mincrmatt12/MSign/esp/main/main.cpp

#include "serial.h"
#include "config.h"
#include "webui.h"
#include "wifitime.h"
#include "upd.h"
#include "sd.h"
#include "config.h"
#include "grabber/grab.h"
#include "webui.cfg.h"

#include <esp_log.h>
#include <esp_system.h>
#include <FreeRTOS.h>
#include <task.h>

#ifndef SIM
#include <esp_wifi.h>
#endif

const static char * const TAG = "app_main";

#ifdef SIM
#define STACK_MULT 8
#else
#define STACK_MULT 1
#endif

int msign_putchar_preservicer(int c) {
	sd::log_putc(c);
#ifdef SIM
	return fputc(c, stderr);
#else
	return putchar(c);
#endif
}

int msign_putchar(int c) {
	sd::log_putc(c);
	if (serial::interface.is_sleeping()) return c;
#ifdef SIM
	return fputc(c, stderr);
#else
	return putchar(c);
#endif
}

extern "C" void app_main() {
	ESP_LOGI(TAG, "Starting MSign...");

	// Try and start the SD layer
	switch (sd::init()) {
		case sd::InitStatus::NoCard:
			ESP_LOGE(TAG, "=============================");
			ESP_LOGE(TAG, "No card is inserted! Halting!");
			ESP_LOGE(TAG, "=============================");
			return;
		case sd::InitStatus::UnusableCard:
		case sd::InitStatus::UnkErr:
			ESP_LOGE(TAG, "Unusable/unknown error while initializing the card.");
			return;
		case sd::InitStatus::FormatError:
			ESP_LOGE(TAG, "No filesystem on card");
			// TODO: maybe indicate these failures to the STM somehow?
			return;
		default:
			break;
	}

	// check for updates
	switch (upd::needed()) {
		case upd::FULL_SYSTEM:
			upd::update_system();
			ESP_LOGW(TAG, "somehow returned from update_system? restarting anyways.");
			esp_restart();
			break;
		case upd::CERTIFICATE_FILE:
			upd::update_cacerts();
			esp_restart();
			break;
		default:
			break;
	}

	// Install logger
	sd::init_logger();
	esp_log_set_putchar(msign_putchar_preservicer);

	bool had_crash = serial::process_stored_crashlogs();
	serial::interface.init();

	esp_log_set_putchar(msign_putchar);

	// Create event handle early
	wifi::events = xEventGroupCreate();
	xEventGroupSetBits(wifi::events, wifi::GrabTaskDead);

	// Start up the servicer
	if (xTaskCreate([](void *ptr){
		serial::interface.run((bool)ptr);
	}, "srv", 2048 * STACK_MULT, (void*)had_crash, 9, NULL) != pdPASS) {
		ESP_LOGE(TAG, "Failed to create srv");
		return;
	}


	// Load the config from the SD card
	if (!config::parse_config_from_sd()) {
		return;
	}

	if (!wifi::init()) {
		ESP_LOGE(TAG, "Not starting data services due to no WIFI.");
		// TODO: make this setup softap mode for netcfg
	}

	// Wait till WIFI is ready to start grab tasks (all for memory optimization crapola in wpa2)
	xEventGroupWaitBits(wifi::events, wifi::WifiConnected, false, true, portMAX_DELAY);

	if (webui::mode != webui::WebuiMode::DISABLED) {
		if (xTaskCreate(webui::run, "webUI", 3072 * STACK_MULT, nullptr,  6, NULL) != pdPASS) {
			ESP_LOGE(TAG, "Failed to create webui; running without it");
		}
	}
	else ESP_LOGW(TAG, "webui is disabled");

	grabber::start();

	ESP_LOGI(TAG, "Created tasks (1)");
	ESP_LOGI(TAG, "Free heap available is %d", (int)heap_caps_get_free_size(pvMALLOC_DRAM));
}
