mincrmatt12/MSign/esp/main/dwhttp.cpp

#include "dwhttp.h"
#include "esp_log.h"
#include <cctype>
#include <cstdio>
#include <esp_system.h>
#include <cstdlib>
#include <memory>
#include <string.h>
#include <bearssl.h>

#include <lwip/sockets.h>
#include <lwip/sys.h>
#include <lwip/netdb.h>

extern "C" {
#include <http_client.h>
#include <http_chunked_recv.h>
};

#include <wpabr_bufman.h>

#include <ff.h>

#undef connect
#undef read
#undef write
#undef socket
#undef send
#undef recv
#undef close
#undef bind

#include "common/ver.h"

// shitty HTTP client....
const char *const msign_ua = "MSign/" MSIGN_MAJOR_VERSION_STRING " (ESP8266, entirely unlike Mozilla) screwanalytics/1.0";

namespace dwhttp {
	namespace detail {
		const static char * const TAG = "d_impl";

		namespace adapter {
			const static char * const TAG = "d_adapter";
			struct HttpAdapter {
				bool connect(const char *host, const char* port="80") {
					if (is_connected()) {
						ESP_LOGW(TAG, "httpadapter still connecting, closing");
						close();
					}

					addrinfo hints{};
					addrinfo *result{}, *rp{};
					hints.ai_family = AF_INET;
					hints.ai_socktype = SOCK_STREAM;

					int stat;
					if ((stat = lwip_getaddrinfo(host, port, &hints, &result))) {
						ESP_LOGE(TAG, "gai fail: %s/%d", lwip_strerr(stat), stat);
						return false;
					}

					for (rp = result; rp != nullptr; rp = rp->ai_next) {
						sockno = lwip_socket(rp->ai_family, rp->ai_socktype,
								rp->ai_protocol);
						if (sockno == -1)
							continue;

						if (lwip_connect(sockno, rp->ai_addr, rp->ai_addrlen) != -1)
							break;                  /* Success */

						lwip_close(sockno);
						sockno = -1;
					}

					lwip_freeaddrinfo(result);

					if (rp == nullptr) {
						ESP_LOGE(TAG, "failed to lookup %s", host);
						return false;
					}

					// Set a 5 second rcvtimeo 
					const struct timeval timeout = { 5, 0 };
					lwip_setsockopt(sockno, SOL_SOCKET, SO_RCVTIMEO, &timeout, sizeof(timeout));

					// We are now connected.
					return true;
				}

				ssize_t read(uint8_t *buf, size_t max) {
					size_t amount = 0;
					while (amount < max) {
						auto amt = read_some(buf, max - amount);
						if (amt == -1) return -1;
						amount += amt;
						buf += amount;
					}
					return amount;
				}

				ssize_t read_some(uint8_t *buf, size_t max) {
					int code = lwip_recv(sockno, buf, max, 0);
					if (code >= 0) return code;
					else {
						switch (errno) {
							default:
								lwip_close(sockno);
								[[fallthrough]];
							case EBADF:
								sockno = -1;
								return -1;
						}
					}
				}

				bool write(const uint8_t *buf, size_t length) {
					size_t pos = 0;
					while (pos < length) {
						int code = lwip_send(sockno, buf + pos, length - pos, 0);
						if (code >= 0) {
							pos += code;
						}
						else {
							switch (errno) {
								default:
									lwip_close(sockno);
									[[fallthrough]];
								case EBADF:
									sockno = -1;
									return false;
							}
						}
					}
					return true;
				}

				bool write(const char *buf) {
					return write((const uint8_t *)buf, strlen(buf));
				}

				void close() {
					if (sockno != -1) lwip_close(sockno);
					sockno = -1;
				}

				void flush() {}

				bool is_connected() {
					return sockno != -1;
				}
			protected:
				int sockno = -1;
			};

			struct HeldTA {
				HeldTA(const char *filename) {
					std::unique_ptr<br_x509_decoder_context> ctx(new br_x509_decoder_context{});
					std::unique_ptr<br_sha256_context> hashet(new br_sha256_context{});

					br_sha256_init(hashet.get());
					br_x509_decoder_init(ctx.get(), (void (*)(void *, const void *, size_t))br_sha256_update, hashet.get());
					FIL certf;

					// Open the file (it's assumed it already exists at this point)
					f_open(&certf, filename, FA_READ);

					// Continue reading in 32 byte chunks
					char buf[32];
					while (!f_eof(&certf)) {
						UINT btr = 0;
						if (f_read(&certf, buf, 32, &btr)) {
							f_close(&certf);
							ESP_LOGE(TAG, "File access in HeldTA failed");
							return;
						}
						br_x509_decoder_push(ctx.get(), buf, btr);
					}

					f_close(&certf);

					br_x509_pkey *pk = br_x509_decoder_get_pkey(ctx.get());
					if (pk == nullptr) {
						ESP_LOGE(TAG, "No pkey in cert!");
						return;
					}

					// Initialize the dn in the TA
					anchor.dn.data = (uint8_t *)malloc(64);
					if (!anchor.dn.data) {
						ESP_LOGE(TAG, "OOM allocating VDN");
						return;
					}
					br_sha256_out(hashet.get(), anchor.dn.data);
					anchor.dn.len = 64;
					anchor.flags = br_x509_decoder_isCA(ctx.get()) ? BR_X509_TA_CA : 0;

					// Extract the public key
					switch (pk->key_type) {
						case BR_KEYTYPE_RSA:
							anchor.pkey.key_type = BR_KEYTYPE_RSA;
							anchor.pkey.key.rsa.n = (uint8_t*)malloc(pk->key.rsa.nlen);
							anchor.pkey.key.rsa.e = (uint8_t*)malloc(pk->key.rsa.elen);
							if ((anchor.pkey.key.rsa.n == nullptr) || (anchor.pkey.key.rsa.e == nullptr)) {
								ESP_LOGE(TAG, "Malloc key elements failed");
								return;
							}
							memcpy(anchor.pkey.key.rsa.n, pk->key.rsa.n, pk->key.rsa.nlen);
							anchor.pkey.key.rsa.nlen = pk->key.rsa.nlen;
							memcpy(anchor.pkey.key.rsa.e, pk->key.rsa.e, pk->key.rsa.elen);
							anchor.pkey.key.rsa.elen = pk->key.rsa.elen;
							is_ok = true;
							return;
						case BR_KEYTYPE_EC:
							anchor.pkey.key_type = BR_KEYTYPE_EC;
							anchor.pkey.key.ec.curve = pk->key.ec.curve;
							anchor.pkey.key.ec.q = (uint8_t*)malloc(pk->key.ec.qlen);
							if (anchor.pkey.key.ec.q == nullptr) {
								ESP_LOGE(TAG, "Malloc key elements failed");
								return;
							}
							memcpy(anchor.pkey.key.ec.q, pk->key.ec.q, pk->key.ec.qlen);
							anchor.pkey.key.ec.qlen = pk->key.ec.qlen;
							is_ok = true;
							return;
						default:
							ESP_LOGE(TAG, "Unknown key type");
							return;
					}
				}
				~HeldTA() {
					ESP_LOGD(TAG, "Freeing TA");
					free(anchor.dn.data);
					if (anchor.pkey.key_type == BR_KEYTYPE_RSA) {
						free(anchor.pkey.key.rsa.n);
						free(anchor.pkey.key.rsa.e);
					} else if (anchor.pkey.key_type == BR_KEYTYPE_EC) {
						free(anchor.pkey.key.ec.q);
					}
				}

				HeldTA(const HeldTA& other) = delete;

				// valid for duration of this class and when is_ok is true
				const br_x509_trust_anchor * get_anchor() {
					if (is_ok) return &anchor;
					else return nullptr;
				}

			private:
				br_x509_trust_anchor anchor{};
				bool is_ok = false;
			};

			struct HttpsAdapter : HttpAdapter {
				bool connect(const char* host) {
					wpa_br_tls_bufs_t buffer_location;
					if (!wpa_br_tls_reserve_buffers(&buffer_location, WPA_BR_TLS_SRC_DWHTTP)) {
						ESP_LOGW(TAG, "unable to reserve ssl buffers from wpa code");
						return false;
					}
					// Try and establish a connection with a socket.
					if (!HttpAdapter::connect(host, "443")) {
						wpa_br_tls_unclaim_buffers(WPA_BR_TLS_SRC_DWHTTP);
						return false;
					}
					// Create all the objects
					ssl_cc = new (std::nothrow) br_ssl_client_context{};
					if (!ssl_cc) {
						wpa_br_tls_unclaim_buffers(WPA_BR_TLS_SRC_DWHTTP);
						ESP_LOGE(TAG, "Out of memory allocating client_context");
						return false;
					}
					ssl_xc = new (std::nothrow) br_x509_minimal_context{};
					if (!ssl_xc) {
						wpa_br_tls_unclaim_buffers(WPA_BR_TLS_SRC_DWHTTP);
						ESP_LOGE(TAG, "Out of memory allocating minimal_context");
						delete ssl_cc; ssl_cc = nullptr;
						return false;
					}
					ssl_ic = new (std::nothrow) br_sslio_context{};
					if (!ssl_ic) {
						wpa_br_tls_unclaim_buffers(WPA_BR_TLS_SRC_DWHTTP);
						ESP_LOGE(TAG, "Out of memory allocating io_context");
						delete ssl_cc; ssl_cc = nullptr;
						delete ssl_xc; ssl_xc = nullptr;
						return false;
					}

					// Begin initializing bearssl
					br_ssl_client_init_full(ssl_cc, ssl_xc, nullptr, 0);

					// Set the buffers
					br_ssl_engine_set_buffers_bidi(&ssl_cc->eng, buffer_location.rx_buf, buffer_location.rx_size, buffer_location.tx_buf, buffer_location.tx_size);
					// Feed some entropy into bearssl
					uint32_t block[8];
					for (int i = 0; i < 8; ++i) block[i] = esp_random();
					br_ssl_engine_inject_entropy(&ssl_cc->eng, &block, sizeof block);
					// Setup certificate verification with our dynamic thingies
					br_x509_minimal_set_dynamic(ssl_xc, this,
						[](void * ptr, void *arg, size_t arg2){
							return ((HttpsAdapter *)ptr)->find_hashed_ta(arg, arg2);
						},
						[](void * ptr, const br_x509_trust_anchor *ta){
							return ((HttpsAdapter *)ptr)->held_ta_free(ta);
						}
					);
					// Copy the host
					active_host = strdup(host);
					// Reset the SSL context
					br_ssl_client_reset(ssl_cc, active_host, 0);
					// Initialize IO
					br_sslio_init(ssl_ic, &ssl_cc->eng, 
						[](void *arg, unsigned char *data, size_t len){
							return ((HttpsAdapter *)arg)->_read(data, len);
						}, this,
						[](void *arg, const unsigned char *data, size_t len){
							return ((HttpsAdapter *)arg)->_write(data, len);
						}, this
					);
					return true;
				}

				ssize_t read(uint8_t *buf, size_t max) {
					if (!is_connected()) return -1;
					int rlen = br_sslio_read_all(ssl_ic, buf, max);
					if (rlen < 0) {
						close();
						return -1;
					}
					return max;
				}

				ssize_t read_some(uint8_t *buf, size_t max) {
					if (!is_connected()) return -1;
					int rlen = br_sslio_read(ssl_ic, buf, max);
					if (rlen < 0) {
						close();
						return -1;
					}
					return rlen;
				}

				bool write(const uint8_t *buf, size_t length) {
					if (!is_connected()) return false;
					int rlen = br_sslio_write_all(ssl_ic, buf, length);
					if (rlen < 0) {
						close();
						return false;
					}
					return true;
				}

				bool write(const char *buf) {
					return write((const uint8_t *)buf, strlen(buf));
				}

				void close() {
					if (is_connected()) {
						// Check error for logging
						int err = br_ssl_engine_last_error(&ssl_cc->eng);
						if (err) ESP_LOGW(TAG, "ssl closing with error %d", err);
						if (err == BR_ERR_IO) ESP_LOGW(TAG, "possible errno %d", errno);
						// Send a close, but ignore it
						br_sslio_close(ssl_ic);
						// Close the underlying socket
						HttpAdapter::close();
						// Only once resources are free actually delete the buffer.
						wpa_br_tls_unclaim_buffers(WPA_BR_TLS_SRC_DWHTTP);
					}
					// Delete all the bearssl objects
					delete ssl_cc;
					delete ssl_xc;
					delete ssl_ic;
					delete held_ta; // should be freed earlier
					free(active_host);
					ssl_cc = nullptr;
					ssl_xc = nullptr;
					ssl_ic = nullptr;
					active_host = nullptr;
					held_ta = nullptr;
				}

				void flush() {
					if (!is_connected()) return;
					br_sslio_flush(ssl_ic);
				}

				bool is_connected() {
					return ssl_cc && ssl_xc && ssl_ic;
				}
			private:
				int _read(unsigned char *buf, size_t len) {
					auto tme = xTaskGetTickCount();

					while (true) {
						ssize_t rlen;

						if (!len) return 0;

						rlen = lwip_recv(this->sockno, buf, len, 0);
						if (rlen <= 0) {
							if (rlen < 0 && (errno == EINTR || errno == EAGAIN)) {
								if (xTaskGetTickCount() - tme > pdMS_TO_TICKS(2500)) {
									ESP_LOGD(TAG, "read timeout");
									return -1;
								}
								continue;
							}
							// don't pollute log for remote closing early
							if (errno != ENOTCONN) ESP_LOGE(TAG, "read failed with errno %d", errno);
							return -1;
						}
						return (int)rlen;
					}
				}

				int _write(const unsigned char *buf, size_t len) {
					while (true) {
						ssize_t wlen;

						if (!len) return 0;

						wlen = lwip_send(this->sockno, buf, len, 0);
						if (wlen <= 0) {
							if (wlen < 0 && (errno == EINTR || errno == EAGAIN)) continue;
							ESP_LOGE(TAG, "write failed with errno %d", errno);
							return -1;
						}
						return (int)wlen;
					}
				}

				const br_x509_trust_anchor * find_hashed_ta(void *hashed_dn, size_t len) {
					if (held_ta) {
						ESP_LOGW(TAG, "didn't free held_ta");
						delete held_ta;
						held_ta = nullptr;
					}

					const static char* prefix = "0:/ca/";

					char buf[256];
					memset(buf, 0, 256);
					strcpy(buf, prefix);

					size_t off = strlen(prefix);

					// Write the hashed_dn as a hex str into the buf
					for (size_t i = 0; i < len; ++i) {
						if (off >= 255) {
							ESP_LOGE(TAG, "hashed_dn is too long to fit in the fn buffer!");
							return nullptr;
						}
						else {
							snprintf(buf + off, 3, "%02x", *((uint8_t *)(hashed_dn) + i));
							off += 2;
						}
					}

					// Check if that file exists
					if (f_stat(buf, nullptr) != FR_OK) {
						ESP_LOGD(TAG, "couldn't find CA file %s", buf);
						return nullptr;
					}

					// Initialize the thing
					held_ta = new HeldTA(buf);
					auto ta = held_ta->get_anchor();
					ESP_LOGD(TAG, "Got trust anchor %p", ta);
					return ta;
				}

				// free
				void held_ta_free(const br_x509_trust_anchor *ta) {
					if (!held_ta) {
						ESP_LOGW(TAG, "unknown held_ta");
					}
					delete held_ta;
					held_ta = nullptr;
				}

				// These are dynamically allocated when a connection is made
				br_ssl_client_context *ssl_cc = nullptr;
				br_x509_minimal_context *ssl_xc = nullptr;
				br_sslio_context *ssl_ic = nullptr;
				char * active_host = nullptr;

				// This is dynamically allocated when requested.
				HeldTA *held_ta = nullptr;
			};
		}

		struct DownloaderBase {
			virtual size_t read_from(uint8_t * buf, size_t max) = 0;
			virtual bool   raw_write(const uint8_t * buf, size_t len) = 0;
			virtual bool   parse_response_headers() = 0;
			virtual void   stop() = 0;

			inline int result_code() const {
				return state.c.result_code;
			}

			inline int content_length() const {
				return state.c.content_length;
			}

			inline bool is_unknown_length() const {
				return (state.c.connection == HTTP_CLIENT_CONNECTION_CLOSE) || state.c.chunked_encoding;
			}

			inline bool is_chunked() const {
				return state.c.chunked_encoding;
			}
		protected:
			http_client_state_t state;
			http_chunked_recv_state_t chunk_state;
			int chunk_counter = 0;
			int remain_bytes = 0;
		};

		template<typename Adapter>
		struct Downloader final : DownloaderBase {
			size_t read_from(uint8_t *buf, size_t max) override {
				if (!socket.is_connected()) return 0;
				if (is_chunked() && chunk_counter && max > chunk_counter) max = chunk_counter;
				int r = socket.read_some(buf, max); // read into the buffer first
				if (r <= 0) {
					ESP_LOGW(TAG, "Read failed from %s", last_server);
					stop();
					return 0;
				}
				if (!is_chunked()) {
					remain_bytes = std::max(0, remain_bytes - r);
					return r;
				}
				else {
					if (chunk_counter == 0) {
						// Try to process the results
						int total_amount = 0;
retry:
						const uint8_t * read_to = buf;
						switch (http_chunked_recv_feed(&read_to, buf + r, &chunk_state)) {
							case HTTP_CHUNKED_RECV_OK: 
								// If we've already read some data but ended in the middle of a chunk, return the total amount read so far.
								if (total_amount) return total_amount;
								// Otherwise, still waiting for end of chunk, grab more data recursively.
								return read_from(buf, max);
							case HTTP_CHUNKED_RECV_DONE:
got_done:
								// End of file, return total amount read so far
								remain_bytes = 0;
								return total_amount;
							case HTTP_CHUNKED_RECV_FAIL:
								// Invalid format
								ESP_LOGW(TAG, "chunked parser threw error");
								return 0;
							case HTTP_CHUNKED_RECV_YIELD_GOT_CHUNK:
								{
									if (chunk_state.c.chunk_size == 0) goto got_done;
									// read_to is now at correct position
									chunk_counter = chunk_state.c.chunk_size;
									// (buf + r) is past-end of read data.
									int remain = (buf + r) - read_to;
									ESP_LOGD(TAG, "got chunk %d %d %d", chunk_counter, total_amount, remain);
									memmove(buf, read_to, remain);
									if (remain <= chunk_counter) {
										chunk_counter -= remain;
										// If we've exactly terminated at a chunk barrier, recurse
										if (total_amount == 0 && remain == 0) {
											return read_from(buf, max);
										}
										else {
											return remain + total_amount;
										}
									}
									else {
										// Advance buf and re-read
										r -= chunk_counter + (read_to - buf);
										buf += chunk_counter;
										total_amount += chunk_counter;
										chunk_counter = 0;
										goto retry;
									}
								}
						}
						ESP_LOGE(TAG, "huh");
						return 0;
					}
					else {
						chunk_counter -= r;
						return r;
					}
				}
			}

			// Close sockets
			void stop() override {
				socket.close();
				last_server = nullptr;
				remain_bytes = 0;
			}
			
			bool start_request(const char *host, const char *path, const char* method) {
				if (socket.is_connected() && (!last_server || strcmp(host, last_server))) {
					ESP_LOGW(TAG, "Socket wasn't closed, closing");
					stop();
				}
				else if (socket.is_connected()) {
					auto tme = xTaskGetTickCount();
					// If there are remaining bytes in the previous transmission, read them.
					while (remain_bytes && socket.is_connected()) {
						uint8_t junk_buf[32];
						ESP_LOGD(TAG, "dumped %d", read_from(junk_buf, 32));
						if (xTaskGetTickCount() - tme > pdMS_TO_TICKS(250)) {
							ESP_LOGW(TAG, "stuck dumping previous connection; reconnecting");
							stop();
							break;
						}
					}
				}
				if (last_server != host || !socket.is_connected()) {
					if (!socket.connect(host)) {
						ESP_LOGE(TAG, "Failed to connect to host");
						return false;
					}
				}
				last_server = host;

				// Initialize http request parser
				http_client_start(&state);

				// Send request
				if (!(socket.write(method) && 
					socket.write(" ") &&
					socket.write(path) &&
					socket.write(" HTTP/1.1\r\n"))) {
					ESP_LOGE(TAG, "Failed to send request path");

					stop();
					return false;
				}

				// Send headers
				if (!(write_header("Host", host) &&
					  write_header("User-Agent", msign_ua))) {

					ESP_LOGE(TAG, "Failed to send request headers");

					stop();
					return false;
				}

				return true;
			}

			bool parse_response_headers() override {
				socket.flush();
				while (true) {
					uint8_t buf;
					int recvd_bytes = socket.read(&buf, 1);
					if (recvd_bytes < 0) {
						ESP_LOGE(TAG, "Got error while recving");
						stop();
						return false;
					}
					// Otherwise, feed it into nmfu
					switch (http_client_feed(&buf, 1 + &buf, &state)) {
						case HTTP_CLIENT_OK:
							continue;
						case HTTP_CLIENT_FAIL:
							ESP_LOGE(TAG, "Parser failed");
							stop();
							return false;
						case HTTP_CLIENT_DONE:
							ESP_LOGD(TAG, "Finished parsing req headers");
							goto finish_req;
					}
				}
finish_req:
				ESP_LOGD(TAG, "Ready with code = %d; length = %d; unklen = %d", result_code(), content_length(), is_unknown_length());
				if (is_chunked()) {
					http_chunked_recv_start(&chunk_state);
					chunk_counter = 0;
					remain_bytes = -1;
				}
				else {
					remain_bytes = content_length();
				}
				return true;
			}

			bool request(const char *host, const char *path, const char* method, const char * const headers[][2], const uint8_t * body=nullptr, const size_t bodylen=0) {
				if (!start_request(host, path, method)) return false;
				// Send body length if present
				if (body) {
					char buf[32];
					snprintf(buf, 32, "%d", (int)bodylen);
					if (!write_header("Content-Length", buf)) {
						ESP_LOGE(TAG, "Failed to send body headers");

						stop();
						return false;
					}
				}

				// Write all provided headers
				for (int i = 0;;++i) {
					if (headers[i][0] == nullptr || headers[i][1] == nullptr) break;
					if (!write_header(headers[i][0], headers[i][1])) {
						ESP_LOGE(TAG, "Failed to send user headers");

						stop();
						return false;
					}
					ESP_LOGD(TAG, "hdr: %s --> %s", headers[i][0], headers[i][1]);
				}

				socket.write("\r\n");
				if (body) {
					if (!socket.write(body, bodylen)) {
						ESP_LOGE(TAG, "Failed to send body");

						stop();
						return false;
					}
				}

				return parse_response_headers();
			}

			bool raw_write(const uint8_t *buf, size_t len) override {
				return socket.write(buf, len);
			}
		private:
			Adapter socket;
			const char * last_server=nullptr;

			bool write_header(const char * name, const char * value) {
				if (!socket.write(name)) return false;
				if (!socket.write(": ")) return false;
				if (!socket.write(value)) return false;
				if (!socket.write("\r\n")) return false;
				return true;
			}
		};

		Downloader<adapter::HttpAdapter> dwnld;
		Downloader<adapter::HttpsAdapter> dwnld_s;

		template<typename T>
		inline constexpr Downloader<T>& get_downloader() {return dwnld;}; 

		template<>
		inline constexpr Downloader<adapter::HttpsAdapter>& get_downloader() {return dwnld_s;};

		template<typename T>
		dwhttp::Download download_with_callback_impl(const char * host, const char * path, const char * const headers[][2], const char * method, const char * body) {
			static auto& dwnld = dwhttp::detail::get_downloader<T>();
			dwnld.request(host, path, method, headers, (const uint8_t *)body, body ? strlen(body) : 0);

			return dwhttp::Download((dwhttp::detail::DownloaderBase *)&dwnld);
		}
		
		template<typename T>
		dwhttp::Connection open_site_impl(const char * host, const char * path, const char *method) {
			static auto& dwnld = dwhttp::detail::get_downloader<T>();
			dwnld.start_request(host, path, method);

			return dwhttp::Connection((dwhttp::detail::DownloaderBase *)&dwnld);
		}
	}
}

dwhttp::Connection dwhttp::open_site(const char * host, const char * path, const char * method) {
	if (host[0] != '_') {
		return detail::open_site_impl<detail::adapter::HttpAdapter>(host, path, method);
	}
	else {
		return detail::open_site_impl<detail::adapter::HttpsAdapter>(++host, path, method);
	}
}

dwhttp::Download dwhttp::download_with_callback(const char * host, const char * path, const char * const headers[][2], const char * method, const char * body) {
	if (host[0] != '_') {
		return detail::download_with_callback_impl<detail::adapter::HttpAdapter>(host, path, headers, method, body);
	}
	else {
		return detail::download_with_callback_impl<detail::adapter::HttpsAdapter>(++host, path, headers, method, body);
	}
}

dwhttp::Download dwhttp::download_with_callback(const char * host, const char * path) {
	static const char * const headers[][2] = {{nullptr, nullptr}};
	return download_with_callback(host, path, headers);
}
dwhttp::Download dwhttp::download_with_callback(const char * host, const char * path, const char * const headers[][2]) {
	return download_with_callback(host, path, headers, "GET", nullptr);
}

dwhttp::Download::~Download() {
	if (adapter) {
		if (!nonclose || (is_unknown_length() && !adapter->is_chunked())) { // unknown_length == connection: close == force stop connection
			adapter->stop();
		}
		adapter = nullptr;
	}
	if (recvbuf) free(recvbuf);
}

int16_t dwhttp::Download::operator()() {
	// Pump recvuf
	if (!recvbuf) {
		recvbuf = (uint8_t *)malloc(32);
		recvpending = 0;
		recvread = 0;
	}
	if (recvread == recvpending) {
		recvpending = adapter->read_from(recvbuf, 32);
		recvread = 0;
	}
	if (recvpending == 0) return -1; // eof
	return recvbuf[recvread++];
}

size_t dwhttp::Download::operator()(uint8_t * buf, size_t amount) {
	size_t r = 0;
	while (recvbuf && recvpending != recvread && amount) {
		auto v = (*this)();
		if (v == -1) return r;
		++r;
		*buf++ = (uint8_t)v;
		--amount;
	}
	r += adapter->read_from(buf, amount);
	return r;
}

int dwhttp::Download::result_code() const {
	return adapter->result_code();
}
int dwhttp::Download::content_length() const {
	return adapter->content_length();
}
bool dwhttp::Download::is_unknown_length() const {
	return adapter->is_unknown_length();
}
void dwhttp::Download::stop() {
	adapter->stop();
}

void dwhttp::close_connection(bool ssl) {
	if (ssl) {
		detail::dwnld_s.stop();
	}
	else {
		detail::dwnld.stop();
	}
}

void dwhttp::Connection::send_header_name(const char* name) {
	uint8_t terminator[2] = {':', ' '};
	adapter->raw_write((const uint8_t *)name, strlen(name));
	adapter->raw_write(terminator, 2);
}

void dwhttp::Connection::send_header_value_part(const char* value, size_t length) {
	adapter->raw_write((const uint8_t *)value, length);
}

void dwhttp::Connection::send_header_end() {
	adapter->raw_write((const uint8_t *)"\r\n", 2);
}

void dwhttp::Connection::start_body(size_t content_length) {
	char sz_buffer[16]; snprintf(sz_buffer, sizeof sz_buffer, "%d", (int)content_length);
	send_header("Content-Length", sz_buffer);
	send_header_end();

	transfer_chunked = false;
	current_state = SEND_BODY;
}

void dwhttp::Connection::start_body() {
	send_header("Transfer-Encoding", "chunked");
	send_header_end();

	transfer_chunked = true;
	current_state = SEND_BODY;
}

void dwhttp::Connection::write(const uint8_t * body, size_t length) {
	if (transfer_chunked) {
		if (!length) return;
		char sz_buffer[16]; snprintf(sz_buffer, sizeof sz_buffer, "%x\r\n", (int)length);
		adapter->raw_write((const uint8_t *)sz_buffer, strlen(sz_buffer));
	}
	adapter->raw_write(body, length);
	if (transfer_chunked) {
		send_header_end();
	}
}

void dwhttp::Connection::end_body() {
	if (current_state != SEND_BODY) {
		send_header_end();
	}
	else if (transfer_chunked) {
		static const char * const end_chunked = "0\r\n\r\n";
		adapter->raw_write((const uint8_t *)end_chunked, strlen(end_chunked));
	}
	if (adapter->parse_response_headers()) {
		current_state = RECEIVE;
	}
	else {
		adapter->stop();
		current_state = CLOSED;
	}
}

size_t dwhttp::url_encoded_size(const char *path, bool ignore_slashes) {
	size_t outsz = 0;
	int c;
	while ((c = *path++)) {
		if (isalnum(c) || c == '~' || c == '-' || c == '.' || c == '_' || (ignore_slashes && c == '/')) ++outsz;
		else outsz += 3;
	}
	return outsz;
}

void dwhttp::url_encode(const char *src, char *target, size_t tgtlen, bool ignore_slashes) {
	int c;
	while (tgtlen > 1 && (c = *src++)) {
		if (isalnum(c) || c == '~' || c == '-' || c == '.' || c == '_' || (ignore_slashes && c == '/')) {
			--tgtlen;
			*target++ = c;
		}
		else {
			if (tgtlen < 4) return;
			snprintf(target, tgtlen, "%%%02X", c);
			tgtlen -= 3;
			target += 3;
		}
		*target = 0;
	}
}
