mincrmatt12/MSign/stm/src/crash/main.h

#ifndef MSN_STCRASH_MAIN_H
#define MSN_STCRASH_MAIN_H

#include <stdint.h>

namespace crash {
	// Transfer control to the crash handler.
	//
	// `errcode` must either be null or point to memory outside of the crash handler's region (i.e.
	// outside VRAM)
	//
	// This function does not return.
	[[noreturn]] void call_crash_main(const char *errcode, uint32_t SP, uint32_t PC, uint32_t LR) __attribute__((naked));

	// Transfer control to the crash handler from an arbitrary point in the code
	[[noreturn]] __attribute__((always_inline)) void inline panic(const char* errcode) {
		uint32_t pc, lr, sp;
		asm volatile (
			"mov %0, pc\n\t"
			"mov %1, lr\n\t"
			"mov %2, sp\n\t" :
			"=r" (pc), "=r" (lr), "=r" (sp)
		);
		call_crash_main(errcode, sp, pc, lr);
	}

	// Transfer control to the crash handler but don't show a backtrace / debug screen, just show a short message and reboot automatically.
	//
	// This is the same as setting PC to 0xffff ffff and SP to 0
	[[noreturn]] void panic_nonfatal(const char* errcode);

	// Transfer control the interrupt handler, getting the state from the stacked registers in an interrupt handler.
	[[noreturn]] void panic_from_isr(const char* errcode, uint32_t *SP_at_ISR_entry);

};

// C exported version of msign::panic
extern "C" void msign_panic(const char *c);

inline void msign_assert(bool c, const char * v) {
	if (!c) msign_panic(v);
}

#endif
