mincrmatt12/MSign/esp/main/sd.h

#ifndef MSN_SD_H
#define MSN_SD_H

#include <ff.h>
#include <FreeRTOS.h>
#include <stream_buffer.h>

namespace sd {
	enum struct InitStatus {
		Ok,
		NoCard,
		FormatError,
		UnusableCard,
		UnkErr
	};

	// Sets up FatFS with this.
	InitStatus init();

	void refresh_log_dir(const char *prefix="log");
	void init_logger();

	void log_putc(char c);

	size_t copy_pending_logs(char *buf, size_t max);

	extern FATFS fs;
}

#endif
