mincrmatt12/MSign/stm/src/protocol.h

#ifndef PROTOCOL_H
#define PROTOCOL_H

#include "common/slots.h"
#include <stdint.h>
#include <FreeRTOS.h>
#include <task.h>

namespace srv {
	enum struct ProtocolState {
		UNINIT,
		HANDSHAKE_RECV,
		HANDSHAKE_SENT,
		UPDATE_STARTING,
		ESP_CRASHED,
		DMA_WAIT_SIZE,
		DMA_GOING
	};

	// Actually does the UART comms with the ESP
	struct ProtocolImpl {
		// Buffers for DMA

		uint8_t dma_buffer[258];
		union {
			uint8_t dma_out_buffer[67]{};
			slots::PacketWrapper<> dma_out_pkt;
		};

		// Implementation
		void setup_uart_dma();
		void send();
		void start_recv(srv::ProtocolState target_state=ProtocolState::DMA_WAIT_SIZE, int offset=0);
		void recv_full();

		// State
		bool is_sending = false;
		ProtocolState state = ProtocolState::UNINIT;
		uint64_t last_comm = 0;
		bool sent_ping = false;
		TaskHandle_t notify_on_send_done = nullptr;

		// Interrupt
		void dma_finish(bool incoming); // returns whether or not we should call process_command
		
		// Switch to "fast mode" for update: 230400 baud
		void switch_fast();

	protected:
		virtual void process_command() = 0;
	};
}

#endif
