mincrmatt12/MSign/stm/src/color.h

#ifndef MSN_COLOR_H
#define MSN_COLOR_H

#include <stdint.h>
#include <utility>
#include <algorithm>

namespace led {
	struct color_t {
		constexpr color_t(uint16_t r, uint16_t g, uint16_t b) :
			r(r), g(g), b(b) {}

		constexpr color_t() : r(0), g(0), b(0) {}
		constexpr color_t(uint16_t gray) : r(gray), g(gray), b(gray) {}

		union {
			struct {
#ifdef USE_F4
				uint16_t r; // minisign panels have order rbg
				uint16_t b;
				uint16_t g;
#else
				uint16_t r;
				uint16_t g;
				uint16_t b;
#endif
			};
			uint16_t components[3];
		};

		uint16_t get_spare() const {
			return ((r & 0xf000) >> 4) | ((g & 0xf000) >> 8) | ((b & 0xf000) >> 12);
		}

		void set_spare(uint16_t value) {
			r = (r & 0x0fff) | (value & 0x0f00) << 4;
			g = (g & 0x0fff) | (value & 0x00f0) << 8;
			b = (b & 0x0fff) | (value & 0x000f) << 12;
		}

#define make_op(x) color_t operator x(const color_t& other) const {return color_t(r x other.r, g x other.g, b x other.b);} \
				   color_t& operator x##= (const color_t& other) {r x##= other.r; g x##= other.g; b x##= other.b; return *this;}

		make_op(+)
		make_op(-)
		make_op(/)
		make_op(*)

#undef make_op

		color_t mix(const color_t& other, uint8_t factor /* from 0-255 */) const {
			return color_t(
				r + ((((int)other.r - (int)this->r) * (int)factor) / 255),
				g + ((((int)other.g - (int)this->g) * (int)factor) / 255),
				b + ((((int)other.b - (int)this->b) * (int)factor) / 255)
			);
		}
	};
}

#endif
