mincrmatt12/MSign/esp/main/webui.cfg.h

#include "config.h"

namespace webui {
	enum struct WebuiMode {
		DISABLED,
		LOCAL,
		PROXIED
	};

	//!cfg: holds .webui.mode, default webui::WebuiMode::LOCAL
	extern WebuiMode mode;

	//!cfg: holds .webui.login.user, default "admin"
	extern config::string_t login_user;

	//!cfg: holds .webui.login.password, default "admin"
	extern config::string_t login_password;
}
