mincrmatt12/MSign/stm/src/crash/rtos.cpp

#include "rtos.h"

#include <FreeRTOS.h>
#include <task.h>

extern bool finished_init_ok;
extern "C" uint8_t _ecstack, _estack;

bool crash::rtos::is_rtos_running() {
	return finished_init_ok;
}

const char* crash::rtos::guess_active_thread_name() {
	// Try and get a TCB pointer
	void * tcb = xTaskGetCurrentTaskHandle();
	// Make sure this pointer makes sense
	if (tcb < &_ecstack || tcb >= &_estack) {
		return nullptr;
	}
	return pcTaskGetName(NULL);
}

void crash::rtos::get_task_regs(uint32_t *topofstack, uint32_t& PC, uint32_t& SP, uint32_t &LR) {
	PC = topofstack[6+8];
	LR = topofstack[5+8];
	bool aligned = topofstack[7+8] & (1 << 9);
	SP = (uint32_t)(&topofstack[8+8]) + aligned * 4;
}
