mincrmatt12/MSign/stm/src/tskmem.cpp

#include "tskmem.h"

namespace tskmem {
	TaskHolder<256> srvc;
	TaskHolder<512> screen;
	TaskHolder<176> dbgtim;
};

// as copied from the docs
extern "C" void vApplicationGetIdleTaskMemory( StaticTask_t **ppxIdleTaskTCBBuffer,
                                    StackType_t **ppxIdleTaskStackBuffer,
                                    uint32_t *pulIdleTaskStackSize )
{
	static StaticTask_t xIdleTaskTCB;
	static StackType_t uxIdleTaskStack[ configMINIMAL_STACK_SIZE ];

    /* Pass out a pointer to the StaticTask_t structure in which the Idle task's
    state will be stored. */
    *ppxIdleTaskTCBBuffer = &xIdleTaskTCB;

    /* Pass out the array that will be used as the Idle task's stack. */
    *ppxIdleTaskStackBuffer = uxIdleTaskStack;

    /* Pass out the size of the array pointed to by *ppxIdleTaskStackBuffer.
    Note that, as the array is necessarily of type StackType_t,
    configMINIMAL_STACK_SIZE is specified in words, not bytes. */
    *pulIdleTaskStackSize = configMINIMAL_STACK_SIZE;
}
