mincrmatt12/MSign/esp/main/upd.h

#ifndef UPD_H
#define UPD_H

namespace upd {
	enum UpdateKind {
		FULL_SYSTEM = 0x01,
		WEB_UI,
		CERTIFICATE_FILE,

		NO_UPDATE = 0x00
	};

	UpdateKind needed(); // is an update needed, based on the state of the SD card
	
	void update_cacerts();
	void update_website();
	void update_system();
}

#endif /* ifndef UPD_H */
