mincrmatt12/MSign/sim/cfg/esp/lwipopts.h

#define LWIP_LWIPOPTS_H
#define SYS_LIGHTWEIGHT_PROT            0
#define NO_SYS                          0
#define MEM_ALIGNMENT                   4U
#define MEM_SIZE                        10240
#define MEMP_NUM_PBUF                   16
#define MEMP_NUM_RAW_PCB                4
#define MEMP_NUM_UDP_PCB                4
#define MEMP_NUM_TCP_PCB                4
#define MEMP_NUM_TCP_PCB_LISTEN         4
#define MEMP_NUM_TCP_SEG                16
#define MEMP_NUM_REASSDATA              1
#define MEMP_NUM_ARP_QUEUE              2
#define MEMP_NUM_SYS_TIMEOUT            8
#define MEMP_NUM_NETBUF                 2
#define MEMP_NUM_NETCONN               32
#define MEMP_NUM_TCPIP_MSG_API          8
#define MEMP_NUM_TCPIP_MSG_INPKT        8
#define PBUF_POOL_SIZE                  8
#define LWIP_ARP                        1
#define TCPIP_THREAD_STACKSIZE 1024
#define TCPIP_THREAD_PRIO 8
#define TCPIP_MBOX_SIZE 6
#define SLIPIF_THREAD_STACKSIZE 1024
#define SLIPIF_THREAD_PRIO 1
#define DEFAULT_THREAD_STACKSIZE 1024
#define DEFAULT_THREAD_PRIO 8
#define DEFAULT_UDP_RECVMBOX_SIZE 6
#define DEFAULT_TCP_RECVMBOX_SIZE 6
#define DEFAULT_ACCEPTMBOX_SIZE 6
#define RECV_BUFSIZE_DEFAULT 2000000000
#define IP_FORWARD                      0
#define IP_OPTIONS_ALLOWED              1
#define IP_REASSEMBLY                   1
#define IP_FRAG                         1
#define IP_REASS_MAXAGE                 3
#define IP_REASS_MAX_PBUFS              4
#define IP_FRAG_USES_STATIC_BUF         0
#define IP_DEFAULT_TTL                  255
#define LWIP_IPV4                  1
#define LWIP_ICMP                       1
#define LWIP_RAW                        1
#define LWIP_DHCP                       1
#define LWIP_AUTOIP                     1
#define LWIP_SNMP                       0
#define LWIP_IGMP                       1
#define LWIP_DNS                        1
#define DNS_TABLE_SIZE                  4
#define DNS_MAX_NAME_LENGTH             256
#define DNS_MAX_SERVERS                 1
#define DNS_FALLBACK_SERVER_INDEX       (DNS_MAX_SERVERS - 1)
#define DNS_DOES_NAME_CHECK             1
#define LWIP_DNS_SECURE (LWIP_DNS_SECURE_RAND_XID | LWIP_DNS_SECURE_NO_MULTIPLE_OUTSTANDING | LWIP_DNS_SECURE_RAND_SRC_PORT)
#define LWIP_DNS_SECURE_RAND_XID                1
#define LWIP_DNS_SECURE_NO_MULTIPLE_OUTSTANDING 2
#define LWIP_DNS_SECURE_RAND_SRC_PORT           4
#define LWIP_UDP                        1
#define LWIP_TCP                        1
#define LWIP_LISTEN_BACKLOG             0
#define PBUF_LINK_HLEN                  16
#define PBUF_POOL_BUFSIZE               LWIP_MEM_ALIGN_SIZE(TCP_MSS+40+PBUF_LINK_HLEN)
#define LWIP_HAVE_LOOPIF                0
#define LWIP_NETCONN                    1
#define LWIP_SOCKET                     1
#define SO_REUSE                        1
#define LWIP_SO_RCVTIMEO           1
#define LWIP_SO_RCVBUF             1
#define LWIP_STATS                      0
#define PPP_SUPPORT                     0
#define LWIP_TCPIP_CORE_LOCKING    1
#define LWIP_COMPAT_SOCKETS 0
