mincrmatt12/MSign/sim/src/esp/esp_log.h

// Copyright 2015-2016 Espressif Systems (Shanghai) PTE LTD
//
// Licensed under the Apache License, Version 2.0 (the "License");
// you may not use this file except in compliance with the License.
// You may obtain a copy of the License at

//     http://www.apache.org/licenses/LICENSE-2.0
//
// Unless required by applicable law or agreed to in writing, software
// distributed under the License is distributed on an "AS IS" BASIS,
// WITHOUT WARRANTIES OR CONDITIONS OF ANY KIND, either express or implied.
// See the License for the specific language governing permissions and
// limitations under the License.

#ifndef __ESP_LOG_H__
#define __ESP_LOG_H__

#include <stdint.h>
#include <stdarg.h>

#ifdef __cplusplus
extern "C" {
#endif

/**
 * @brief Log level
 *
 */
typedef enum {
    ESP_LOG_NONE = 0,   /*!< No log output */
    ESP_LOG_ERROR,      /*!< Critical errors, software module can not recover on its own */
    ESP_LOG_WARN,       /*!< Error conditions from which recovery measures have been taken */
    ESP_LOG_INFO,       /*!< Information messages which describe normal flow of events */
    ESP_LOG_DEBUG,      /*!< Extra information which is not necessary for normal use (values, pointers, sizes, etc). */
    ESP_LOG_VERBOSE,    /*!< Bigger chunks of debugging information, or frequent messages which can potentially flood the output. */

    ESP_LOG_MAX
} esp_log_level_t;

typedef int (*putchar_like_t)(int ch);

#define esp_log_level_set(tag, level)

/**
 * @brief Set function used to output log entries
 *
 * By default, log output goes to UART0. This function can be used to redirect log
 * output to some other destination, such as file or network. Returns the original
 * log handler, which may be necessary to return output to the previous destination.
 *
 * @param func new Function used for output. Must have same signature as putchar.
 *
 * @return func old Function used for output.
 */
putchar_like_t esp_log_set_putchar(putchar_like_t func);

/**
 * @brief Function which returns timestamp to be used in log output
 *
 * This function is used in expansion of ESP_LOGx macros.
 * In the 2nd stage bootloader, and at early application startup stage
 * this function uses CPU cycle counter as time source. Later when
 * FreeRTOS scheduler start running, it switches to FreeRTOS tick count.
 *
 * For now, we ignore millisecond counter overflow.
 *
 * @return timestamp, in milliseconds
 */
uint32_t esp_log_timestamp(void);

#define esp_log_early_timestamp esp_log_timestamp

/**
 * @brief Write message into the log
 *
 * This function is not intended to be used directly. Instead, use one of
 * ESP_LOGE, ESP_LOGW, ESP_LOGI, ESP_LOGD, ESP_LOGV macros.
 *
 * This function or these macros should not be used from an interrupt.
 */
void esp_log_write(esp_log_level_t level, const char* tag, const char* format, ...) /*__attribute__ ((format (printf, 3, 4)))*/;

#define esp_early_log_write esp_log_write

/** @cond */

#define LOG_LOCAL_LEVEL ESP_LOG_DEBUG

/** @endcond */

//to be back compatible
#define esp_log_buffer_hex      ESP_LOG_BUFFER_HEX
#define esp_log_buffer_char     ESP_LOG_BUFFER_CHAR

#if CONFIG_LOG_COLORS
#define LOG_COLOR_BLACK   "30"
#define LOG_COLOR_RED     "31"
#define LOG_COLOR_GREEN   "32"
#define LOG_COLOR_BROWN   "33"
#define LOG_COLOR_BLUE    "34"
#define LOG_COLOR_PURPLE  "35"
#define LOG_COLOR_CYAN    "36"
#define LOG_COLOR(COLOR)  "\033[0;" COLOR "m"
#define LOG_BOLD(COLOR)   "\033[1;" COLOR "m"
#define LOG_RESET_COLOR   "\033[0m"
#define LOG_COLOR_E       LOG_COLOR(LOG_COLOR_RED)
#define LOG_COLOR_W       LOG_COLOR(LOG_COLOR_BROWN)
#define LOG_COLOR_I       LOG_COLOR(LOG_COLOR_GREEN)
#define LOG_COLOR_D
#define LOG_COLOR_V
#else //CONFIG_LOG_COLORS
#define LOG_COLOR_E
#define LOG_COLOR_W
#define LOG_COLOR_I
#define LOG_COLOR_D
#define LOG_COLOR_V
#define LOG_RESET_COLOR
#endif //CONFIG_LOG_COLORS

/** @endcond */

/// macro to output logs in startup code, before heap allocator and syscalls have been initialized. log at ``ESP_LOG_ERROR`` level. @see ``printf``,``ESP_LOGE``
#define ESP_EARLY_LOGE( tag, format, ... ) ESP_LOG_EARLY_IMPL(tag, format, ESP_LOG_ERROR,   E, ##__VA_ARGS__)
/// macro to output logs in startup code at ``ESP_LOG_WARN`` level.  @see ``ESP_EARLY_LOGE``,``ESP_LOGE``, ``printf``
#define ESP_EARLY_LOGW( tag, format, ... ) ESP_LOG_EARLY_IMPL(tag, format, ESP_LOG_WARN,    W, ##__VA_ARGS__)
/// macro to output logs in startup code at ``ESP_LOG_INFO`` level.  @see ``ESP_EARLY_LOGE``,``ESP_LOGE``, ``printf``
#define ESP_EARLY_LOGI( tag, format, ... ) ESP_LOG_EARLY_IMPL(tag, format, ESP_LOG_INFO,    I, ##__VA_ARGS__)
/// macro to output logs in startup code at ``ESP_LOG_DEBUG`` level.  @see ``ESP_EARLY_LOGE``,``ESP_LOGE``, ``printf``
#define ESP_EARLY_LOGD( tag, format, ... ) ESP_LOG_EARLY_IMPL(tag, format, ESP_LOG_DEBUG,   D, ##__VA_ARGS__)
/// macro to output logs in startup code at ``ESP_LOG_VERBOSE`` level.  @see ``ESP_EARLY_LOGE``,``ESP_LOGE``, ``printf``
#define ESP_EARLY_LOGV( tag, format, ... ) ESP_LOG_EARLY_IMPL(tag, format, ESP_LOG_VERBOSE, V, ##__VA_ARGS__)

#define ESP_LOG_EARLY_IMPL(tag, format, log_level, log_tag_letter, ...) do {                         \
        if (LOG_LOCAL_LEVEL >= log_level) {                                                          \
            esp_early_log_write(log_level, tag, format, ##__VA_ARGS__);                              \
        }} while(0)

#ifndef BOOTLOADER_BUILD
#define ESP_LOGE( tag, format, ... ) ESP_LOG_LEVEL_LOCAL(ESP_LOG_ERROR,   tag, format, ##__VA_ARGS__)
#define ESP_LOGW( tag, format, ... ) ESP_LOG_LEVEL_LOCAL(ESP_LOG_WARN,    tag, format, ##__VA_ARGS__)
#define ESP_LOGI( tag, format, ... ) ESP_LOG_LEVEL_LOCAL(ESP_LOG_INFO,    tag, format, ##__VA_ARGS__)
#define ESP_LOGD( tag, format, ... ) ESP_LOG_LEVEL_LOCAL(ESP_LOG_DEBUG,   tag, format, ##__VA_ARGS__)
#define ESP_LOGV( tag, format, ... ) ESP_LOG_LEVEL_LOCAL(ESP_LOG_VERBOSE, tag, format, ##__VA_ARGS__)
#else
/**
 * macro to output logs at ESP_LOG_ERROR level.
 *
 * @param tag tag of the log, which can be used to change the log level by ``esp_log_level_set`` at runtime.
 *
 * @see ``printf``
 */
#define ESP_LOGE( tag, format, ... )  ESP_EARLY_LOGE(tag, format, ##__VA_ARGS__)
/// macro to output logs at ``ESP_LOG_WARN`` level.  @see ``ESP_LOGE``
#define ESP_LOGW( tag, format, ... )  ESP_EARLY_LOGW(tag, format, ##__VA_ARGS__)
/// macro to output logs at ``ESP_LOG_INFO`` level.  @see ``ESP_LOGE``
#define ESP_LOGI( tag, format, ... )  ESP_EARLY_LOGI(tag, format, ##__VA_ARGS__)
/// macro to output logs at ``ESP_LOG_DEBUG`` level.  @see ``ESP_LOGE``
#define ESP_LOGD( tag, format, ... )  ESP_EARLY_LOGD(tag, format, ##__VA_ARGS__)
/// macro to output logs at ``ESP_LOG_VERBOSE`` level.  @see ``ESP_LOGE``
#define ESP_LOGV( tag, format, ... )  ESP_EARLY_LOGV(tag, format, ##__VA_ARGS__)
#endif  // BOOTLOADER_BUILD

/** runtime macro to output logs at a specified level.
 * 
 * @param tag tag of the log, which can be used to change the log level by ``esp_log_level_set`` at runtime.
 * @param level level of the output log.
 * @param format format of the output log. see ``printf``
 * @param ... variables to be replaced into the log. see ``printf``
 *
 * @see ``printf``
 */
#define ESP_LOG_LEVEL(level, tag, format, ...) do {                     \
        if (level==ESP_LOG_ERROR )          { esp_log_write(ESP_LOG_ERROR,      tag, format, ##__VA_ARGS__); } \
        else if (level==ESP_LOG_WARN )      { esp_log_write(ESP_LOG_WARN,       tag, format, ##__VA_ARGS__); } \
        else if (level==ESP_LOG_DEBUG )     { esp_log_write(ESP_LOG_DEBUG,      tag, format, ##__VA_ARGS__); } \
        else if (level==ESP_LOG_VERBOSE )   { esp_log_write(ESP_LOG_VERBOSE,    tag, format, ##__VA_ARGS__); } \
        else                                { esp_log_write(ESP_LOG_INFO,       tag, format, ##__VA_ARGS__); } \
    } while(0)

/** runtime macro to output logs at a specified level. Also check the level with ``LOG_LOCAL_LEVEL``.
 *
 * @see ``printf``, ``ESP_LOG_LEVEL``
 */
#define ESP_LOG_LEVEL_LOCAL(level, tag, format, ...) do {               \
        if ( LOG_LOCAL_LEVEL >= level ) ESP_LOG_LEVEL(level, tag, format, ##__VA_ARGS__); \
    } while(0)

#ifdef __cplusplus
}
#endif


#endif /* __ESP_LOG_H__ */
